JamesStokebrand/RGB_LED_Controller_HW_SW_V1/src_code/mcu_sleep_class.cpp

/****************************************************
    MCU Sleep Class

    File:   mcu_sleep_class.cpp
    Author: James Stokebrand
    jamesstokebrand AT gmail DOT com

    mcu_sleep_class.cpp file is part of the RGB LED Controller and Node 
     version 1 hardware project.

    This file contains the code to sleep the ATmaga328p chip.
    There are two parts:  
     - The PRR (power reduction register) which is used to dynamically
        turn off unused hardware interfaces (IE TWI,SPI,Timers etc)
     - Safely set_sleep_mode() method.
     
    Copyright (C) 2015 - James Stokebrand - 2015 Mar 12

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
    Rev History:
     When         Who                Description of change
    -----------  ----------         ------------------------
    2014 Nov 18  James Stokebrand   Initial creation.

*****************************************************/

#ifndef _MCU_SLEEP_CLASS_H_
#include "mcu_sleep_class.h"
#endif

mcu_sleep_class* mcu_sleep_class::m_pInstance = nullptr;

mcu_sleep_class* mcu_sleep_class::getInstance()
{
    return m_pInstance ? m_pInstance : (m_pInstance = new mcu_sleep_class);
}

void mcu_sleep_class::DisableSleep()
{
    // Prevent the MCU to go into sleep mode.
    _AllowSleep = false;
}

void mcu_sleep_class::EnableSleep()
{
    // Allow the MCU to go into sleep mode.
    _AllowSleep = true;
}


// These methods enable/disable the status LED during sleep
//  for debugging needs

// Disable status LED
void mcu_sleep_class::DisableStatusLED() {
    // Disable Status LED.
    _EnableStatusLED = false;
    SleepStatusLED.Off();
}

// Enable status LED
void mcu_sleep_class::EnableStatusLED() {
    // Enable Status LED.
    _EnableStatusLED = true;
    SleepStatusLED.On();
}


void mcu_sleep_class::SetSleepMode(E_PowerSleepMode const &A)
{
    // External interface to update/change the sleep mode
    _PowerSleepMode = A;    
}


void mcu_sleep_class::SetInterfaceUsage(E_PowerUsage const &_Interface, E_PowerInterfaceInUse const &_InUse)
{
    // If we didn't enable sleeping ... dont bother to set the bits.
    if (!_AllowSleep) return;

    // Individual modules will register with the sleep class
    //  to notify it that the interface is in use.
    if (_InUse == E_POWER_INTERFACE_DISABLE_POWER_SAVINGS) {
        // Interface is in use.  Set bit to 0(Zero) to enable
        //  and turn on the interface. 
        // IE  Interface is in USE!  Using power.  Dont want to sleep!
        _power_reduction_variable &= ~(1<<_Interface);
    } else if (_InUse == E_POWER_INTERFACE_ENABLE_POWER_SAVINGS) {
        // Interface is no longer in use.  Set to 1(one) to 
        //  turn off the interface to save power.
        // IE  Interface is *NOT* in use!  Turn it off to save power.
        _power_reduction_variable |= (1<<_Interface);
    }

    // Set the PRR
    PRR = _power_reduction_variable;
}

void mcu_sleep_class::GoMakeSleepNow()
{
    // Didn't enable sleep!  Just return.
    if (!_AllowSleep) return;

    // Possible power sleep mode types for the ATmega328p:
    //   SLEEP_MODE_IDLE - works
    //   SLEEP_MODE_ADC
    //   SLEEP_MODE_PWR_DOWN
    //   SLEEP_MODE_PWR_SAVE
    //   SLEEP_MODE_STANDBY
    //   SLEEP_MODE_EXT_STANDBY

    // select POWER SAVE mode before sleeping
    switch (_PowerSleepMode)
    {
    case E_MCU_SLEEP_MODE_IDLE:
        // This is the default
        set_sleep_mode(SLEEP_MODE_IDLE);
    break;
    case E_MCU_SLEEP_MODE_ADC:
        set_sleep_mode(SLEEP_MODE_ADC);
    break;
    case E_MCU_SLEEP_MODE_PWR_DOWN:
        set_sleep_mode(SLEEP_MODE_PWR_DOWN);
    break;
    case E_MCU_SLEEP_MODE_PWR_SAVE:
        set_sleep_mode(SLEEP_MODE_PWR_SAVE);
    break;
    case E_MCU_SLEEP_MODE_STANDBY:
        set_sleep_mode(SLEEP_MODE_STANDBY);
    break;
    case E_MCU_SLEEP_MODE_EXT_STANDBY:
        set_sleep_mode(SLEEP_MODE_EXT_STANDBY);
    break;
    default:
        // Do nothing in this case.
    break;
    }

    cli();
    sleep_enable();
    sleep_bod_disable();

    // Toggle the status LED if enabled.
    if (_EnableStatusLED) SleepStatusLED.Toggle();

    sei();
    sleep_cpu();

    // ######################################
    // Have entered sleep here.
    // ######################################

    // Toggle the status LED if enabled.
    if (_EnableStatusLED) SleepStatusLED.Toggle();

    sleep_disable();
    sei();
}

void mcu_sleep_class::SetInputAndPullupResistor(IOPinDefines::E_PinDef const &A)
{
    // Didn't enable sleep!  Just return.
    if (!_AllowSleep) return;

    // This doesn't save much power ... but every little 
    //   bit helps.

    // To save power:
    //  Set unused pin as input
    //  Activate pull up resistor
    IOPinDefines temp(A);

    // Set pin as input
    *(temp._DDRReg) &= ~(1<<temp._Bit);

    // Activate pull up resistor
    *(temp._PortReg) |= (1<<temp._Bit);
}
